christofteuscher/TrailNapAlarm/openchoice/Limiter50ohm10mVpp.bmp

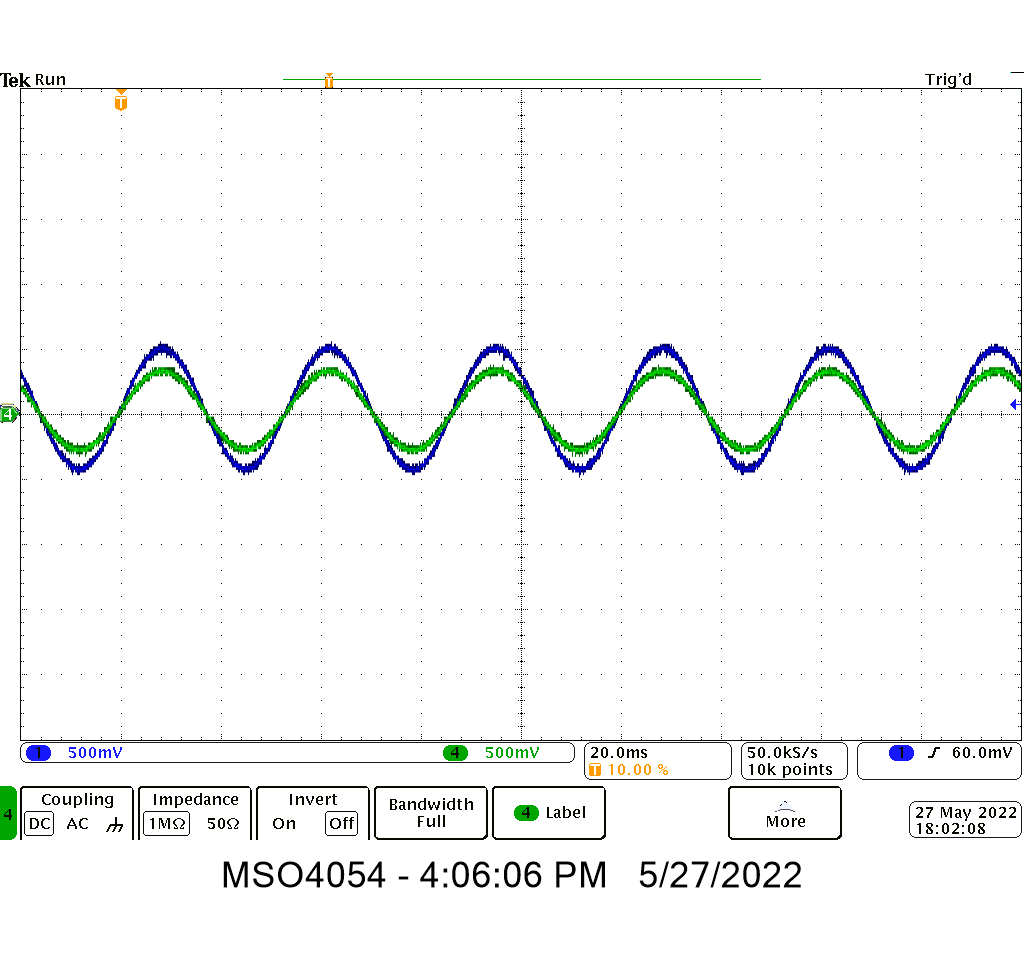
openchoice/Limiter50ohm10mVpp.bmp
