christofteuscher/TrailNapAlarm/res/figures/docFigs/AD620_example.png

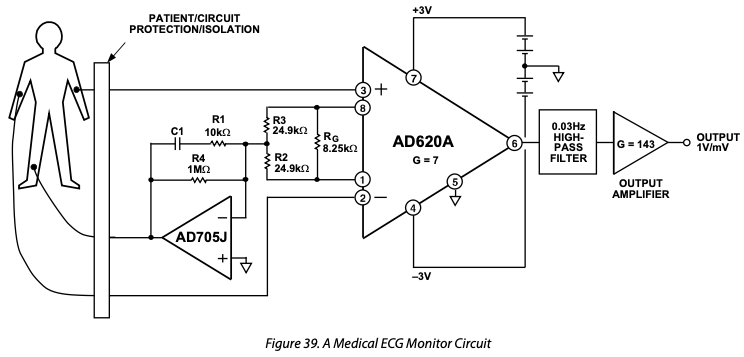
res/figures/docFigs/AD620_example.png
