christofteuscher/TrailNapAlarm/res/figures/docFigs/adc_breakout_connections.PNG

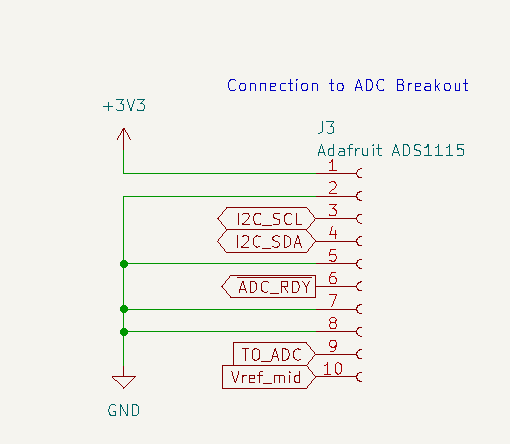
res/figures/docFigs/adc_breakout_connections.PNG
