christofteuscher/TrailNapAlarm/res/figures/docFigs/amplifier-filter.png

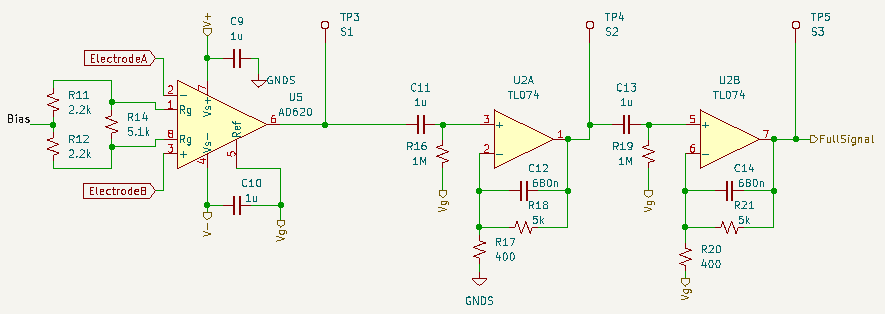
res/figures/docFigs/amplifier-filter.png
