christofteuscher/TrailNapAlarm/res/figures/docFigs/CapstoneEEGL0_L1.png

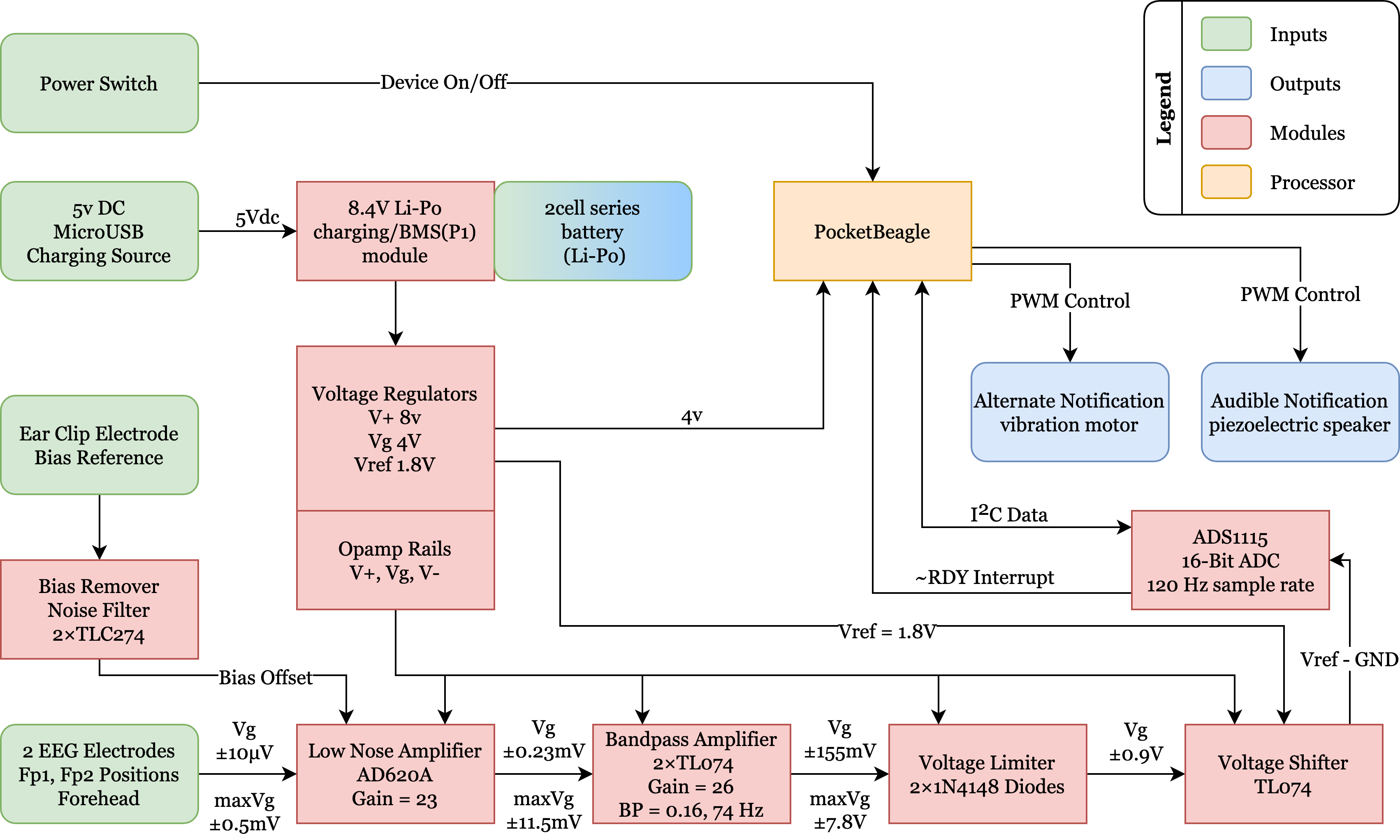
res/figures/docFigs/CapstoneEEGL0_L1.png
