christofteuscher/TrailNapAlarm/res/figures/docFigs/comparisonfig.png

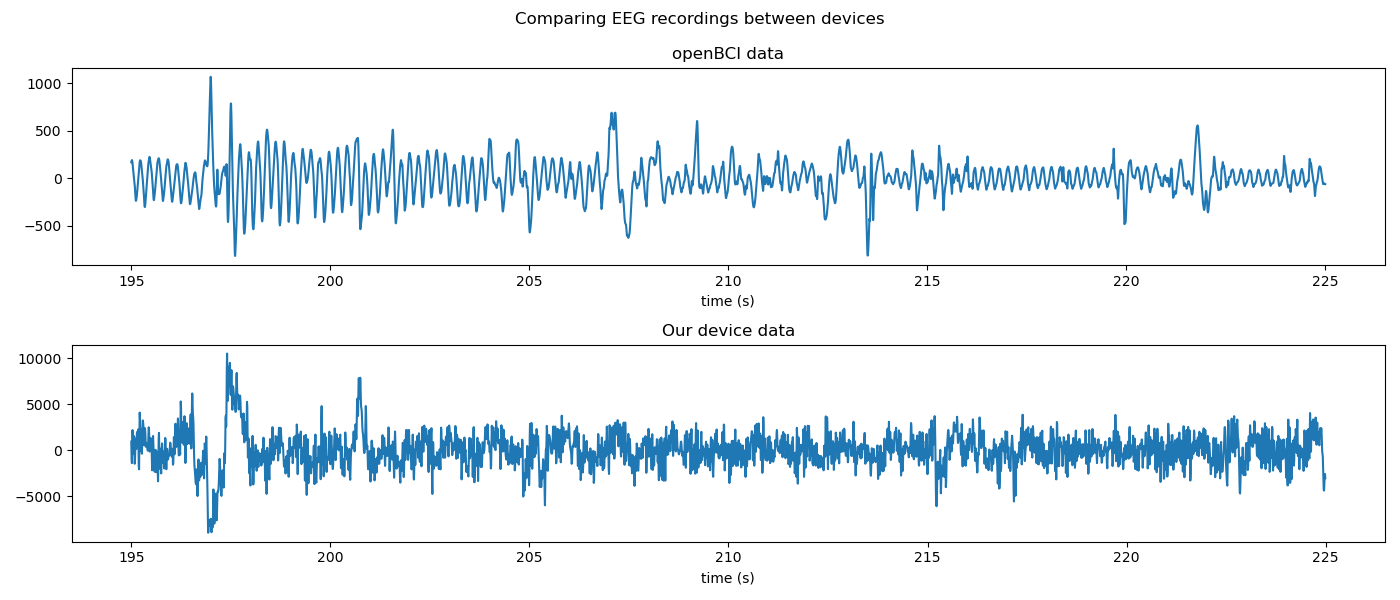
res/figures/docFigs/comparisonfig.png
