christofteuscher/TrailNapAlarm/res/figures/docFigs/dataFlowDiag.png

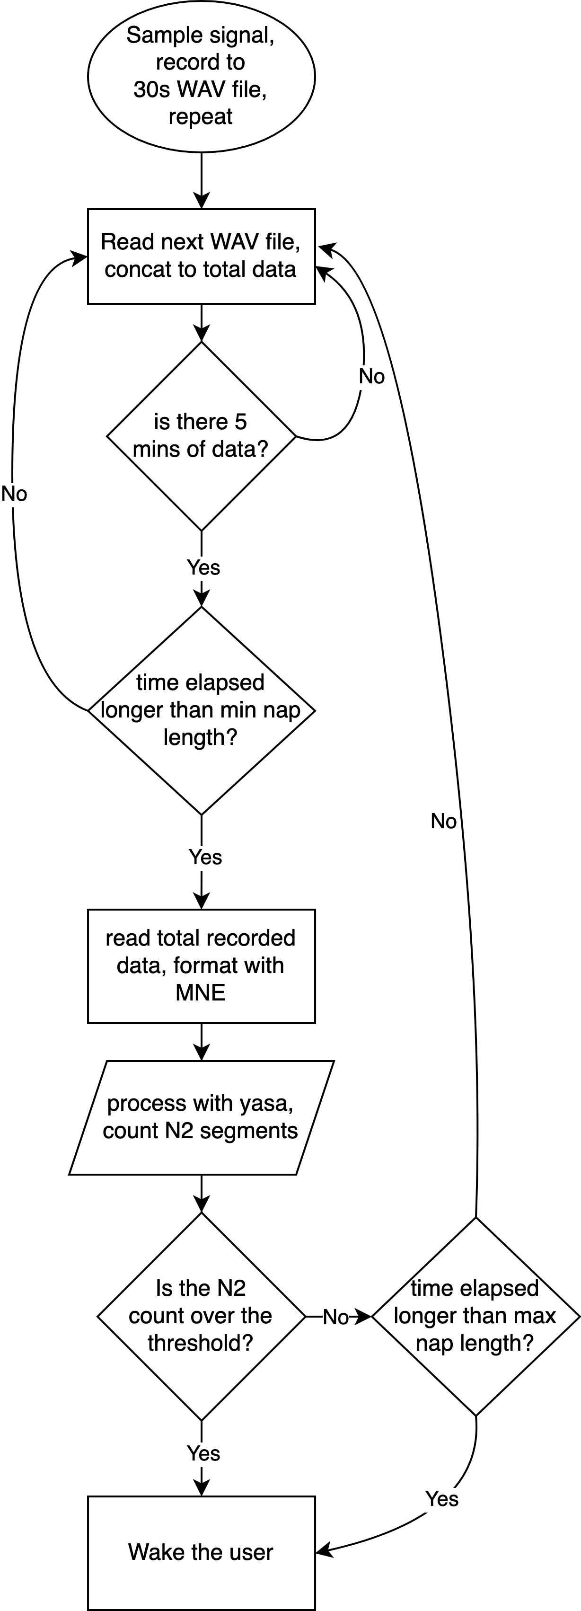
res/figures/docFigs/dataFlowDiag.png
