christofteuscher/TrailNapAlarm/res/figures/docFigs/drl_ckt.png

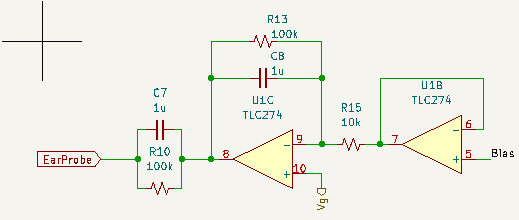
res/figures/docFigs/drl_ckt.png
