christofteuscher/TrailNapAlarm/res/figures/docFigs/EEG.png

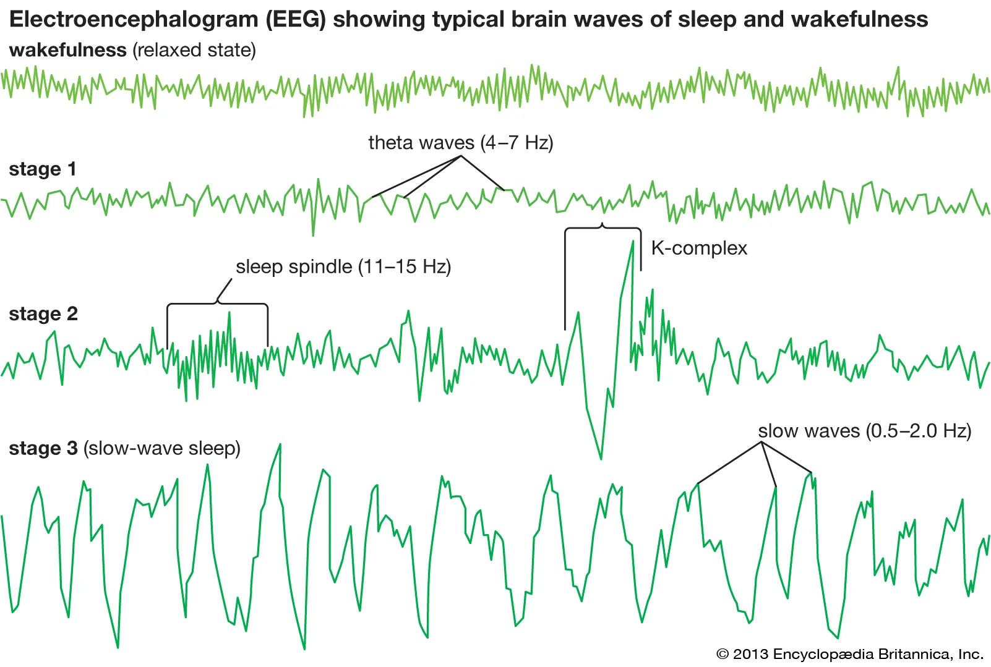
res/figures/docFigs/EEG.png
