christofteuscher/TrailNapAlarm/res/figures/docFigs/power_rails.PNG

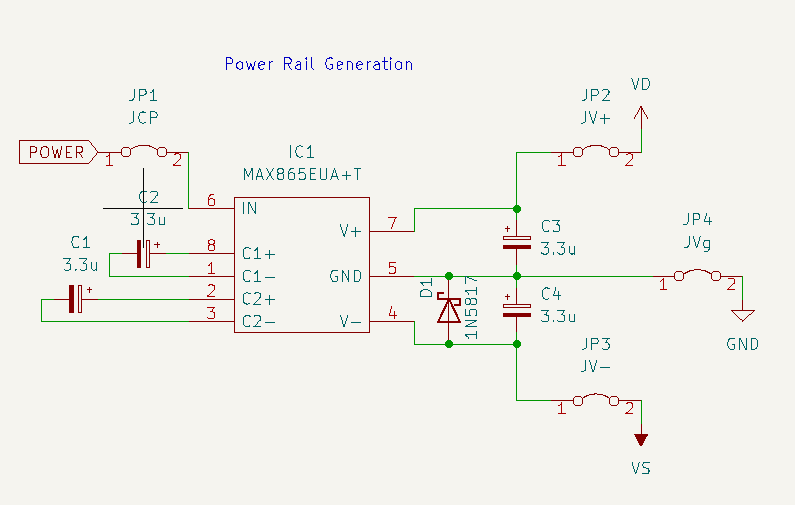
res/figures/docFigs/power_rails.PNG
