christofteuscher/TrailNapAlarm/res/figures/docFigs/spindledetect.png

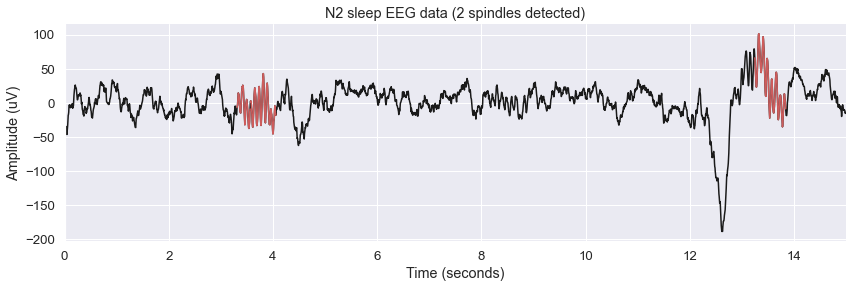
res/figures/docFigs/spindledetect.png
