christofteuscher/TrailNapAlarm/res/figures/docFigs/teuscherlab.png

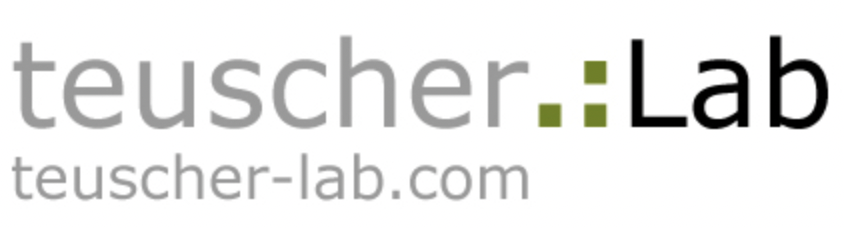
res/figures/docFigs/teuscherlab.png
