christofteuscher/TrailNapAlarm/res/figures/docFigs/timeseries_stages.png

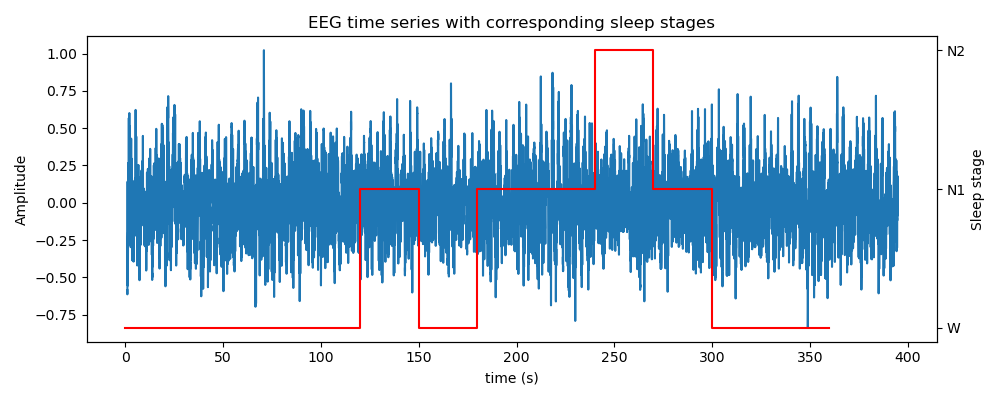
res/figures/docFigs/timeseries_stages.png
