christofteuscher/TrailNapAlarm/res/figures/docFigs/voltageshifter.png

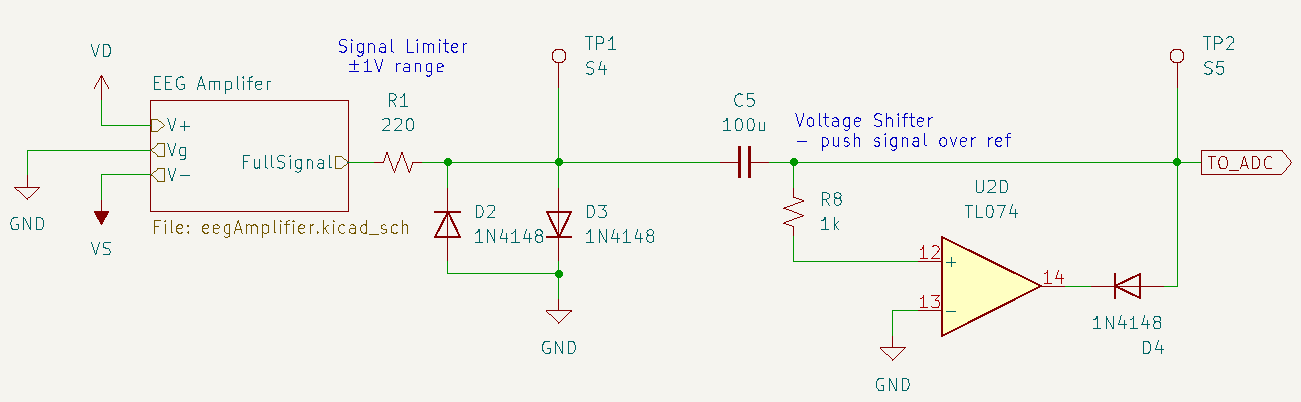
res/figures/docFigs/voltageshifter.png
