christofteuscher/TrailNapAlarm/res/figures/exampleYasafigs/Fz_10_movcorrel.png

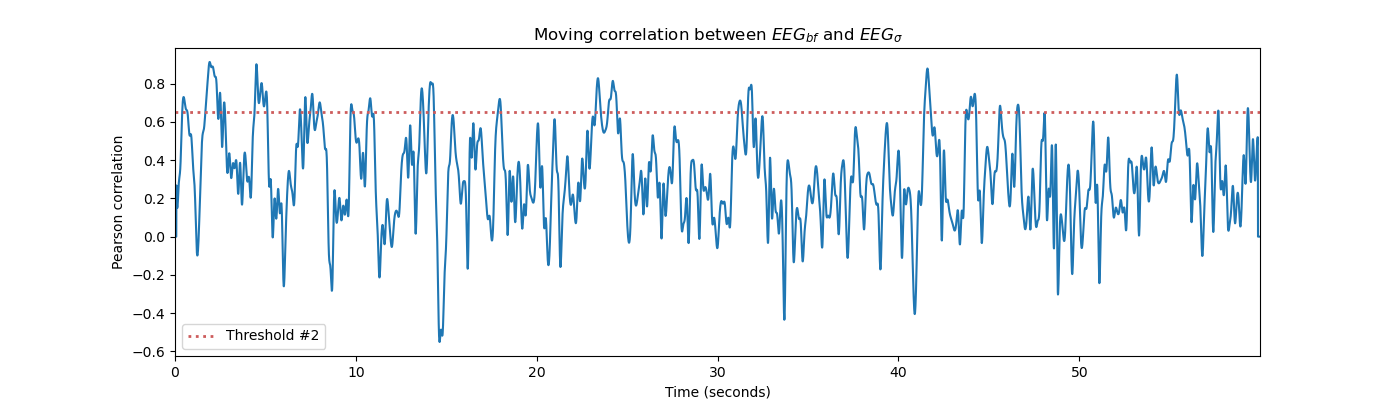
res/figures/exampleYasafigs/Fz_10_movcorrel.png
