christofteuscher/TrailNapAlarm/res/figures/exampleYasafigs/Fz_10_sigma_rel_power.png

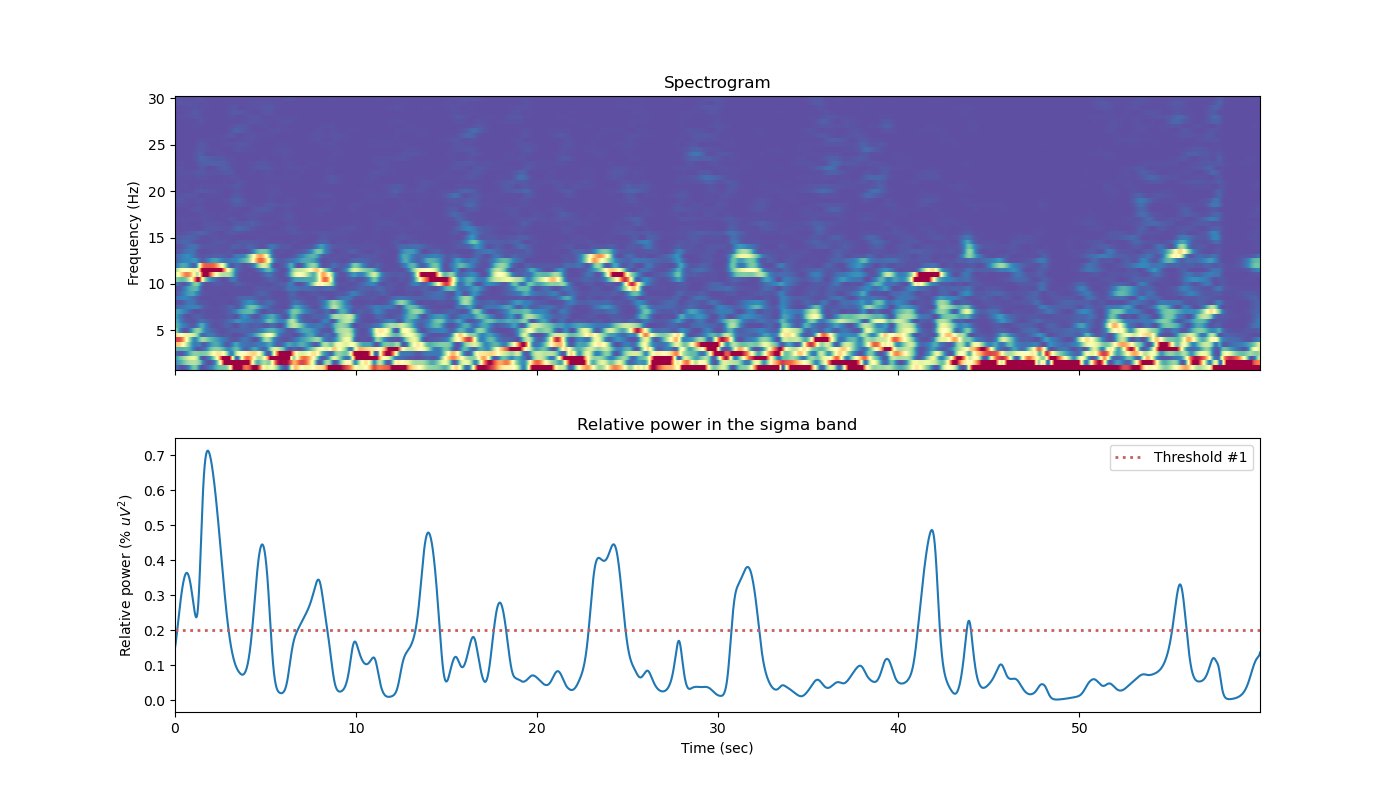
res/figures/exampleYasafigs/Fz_10_sigma_rel_power.png
