christofteuscher/TrailNapAlarm/res/figures/exampleYasafigs/Fz_10_timeseries.png

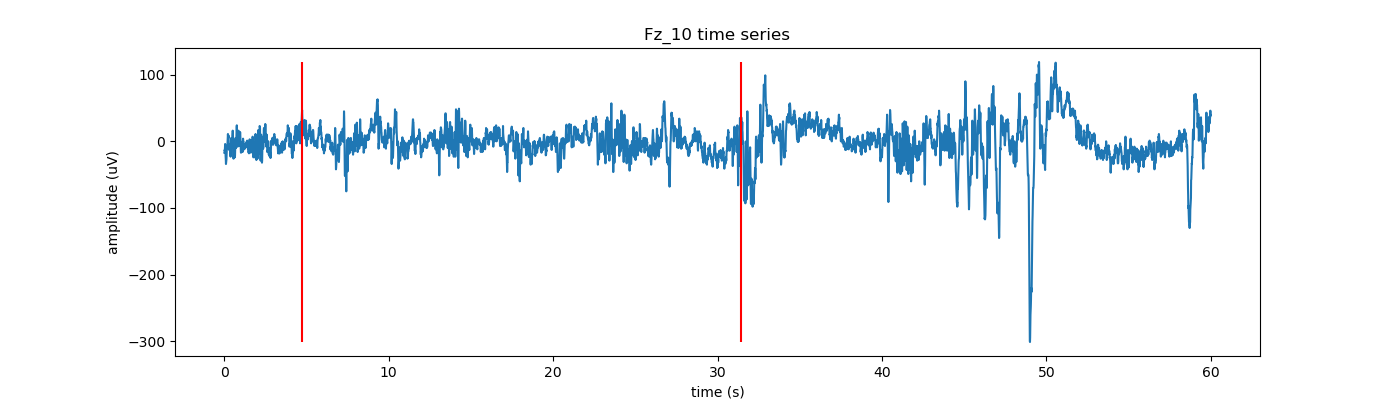
res/figures/exampleYasafigs/Fz_10_timeseries.png
