christofteuscher/TrailNapAlarm/openchoice/TestCheckClamperOutput.bmp

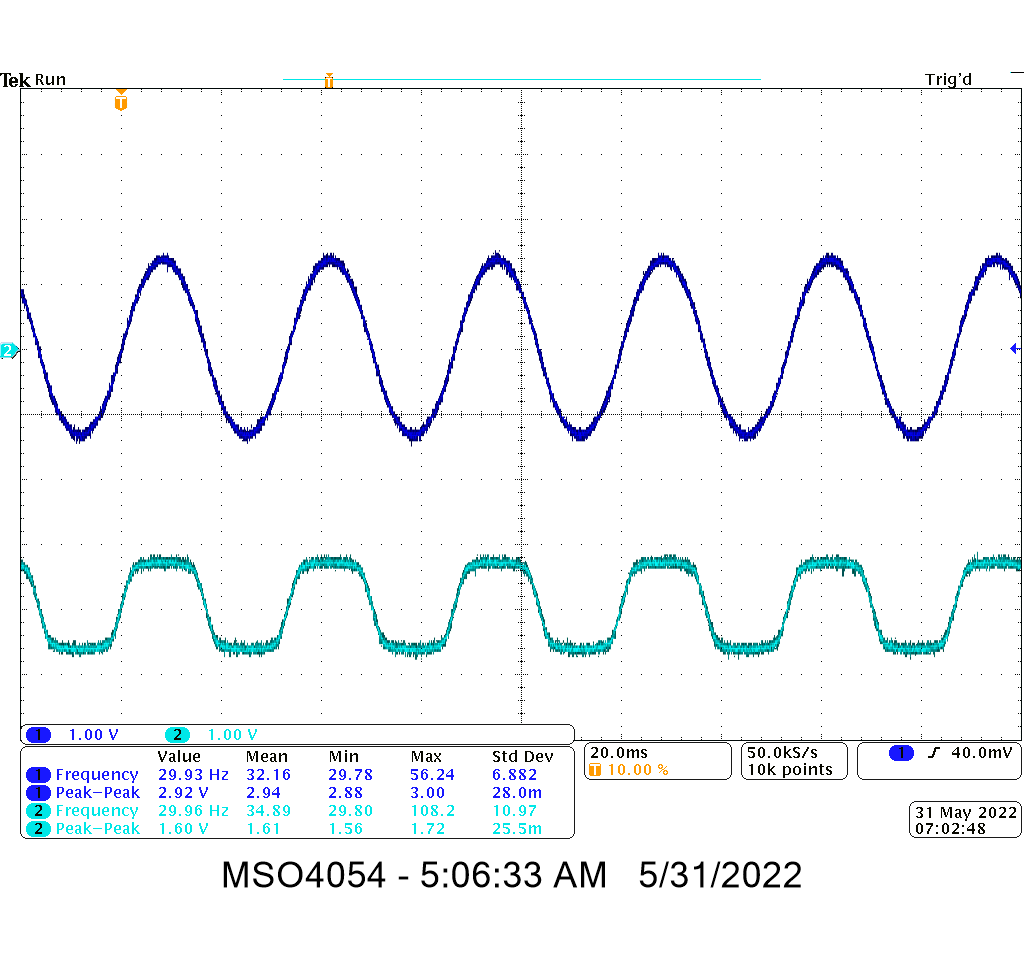
openchoice/TestCheckClamperOutput.bmp
