christofteuscher/TrailNapAlarm/openchoice/TestInputBase.bmp

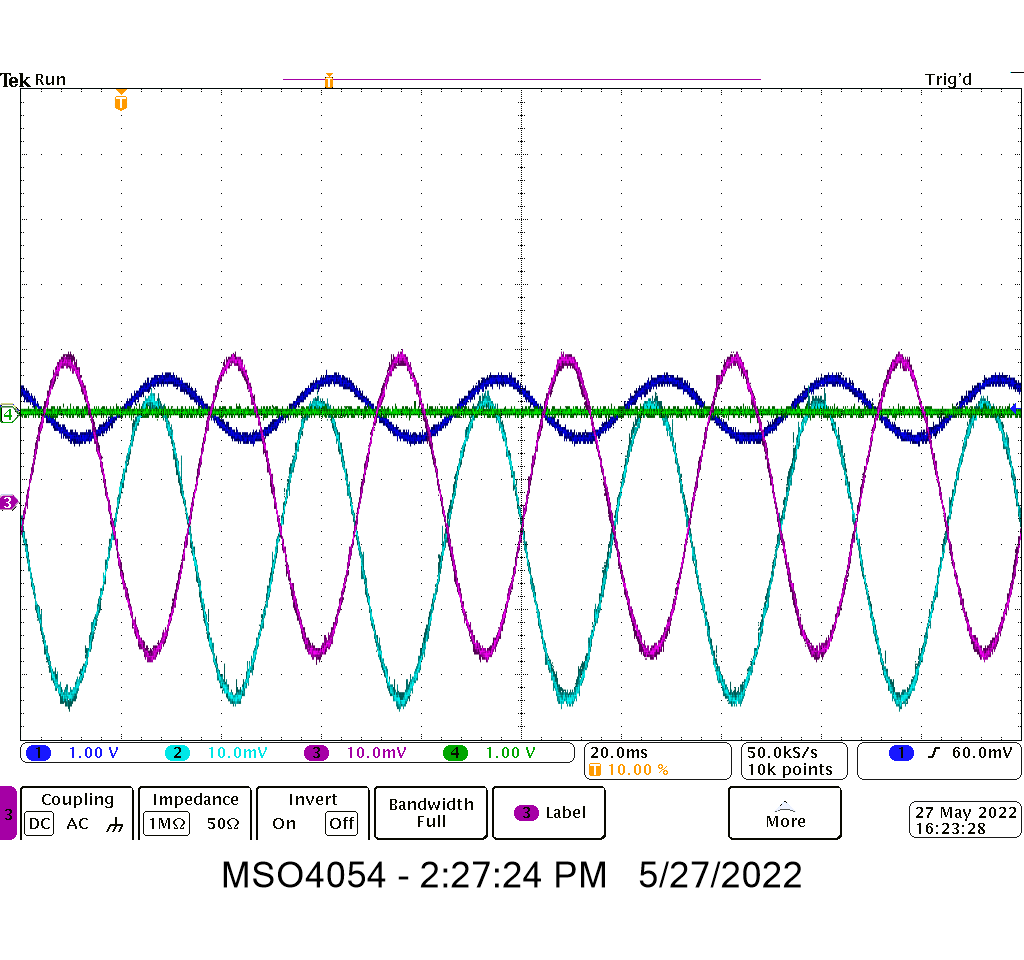
openchoice/TestInputBase.bmp
