christofteuscher/TrailNapAlarm/openchoice/TestInputBaseLimiter.bmp

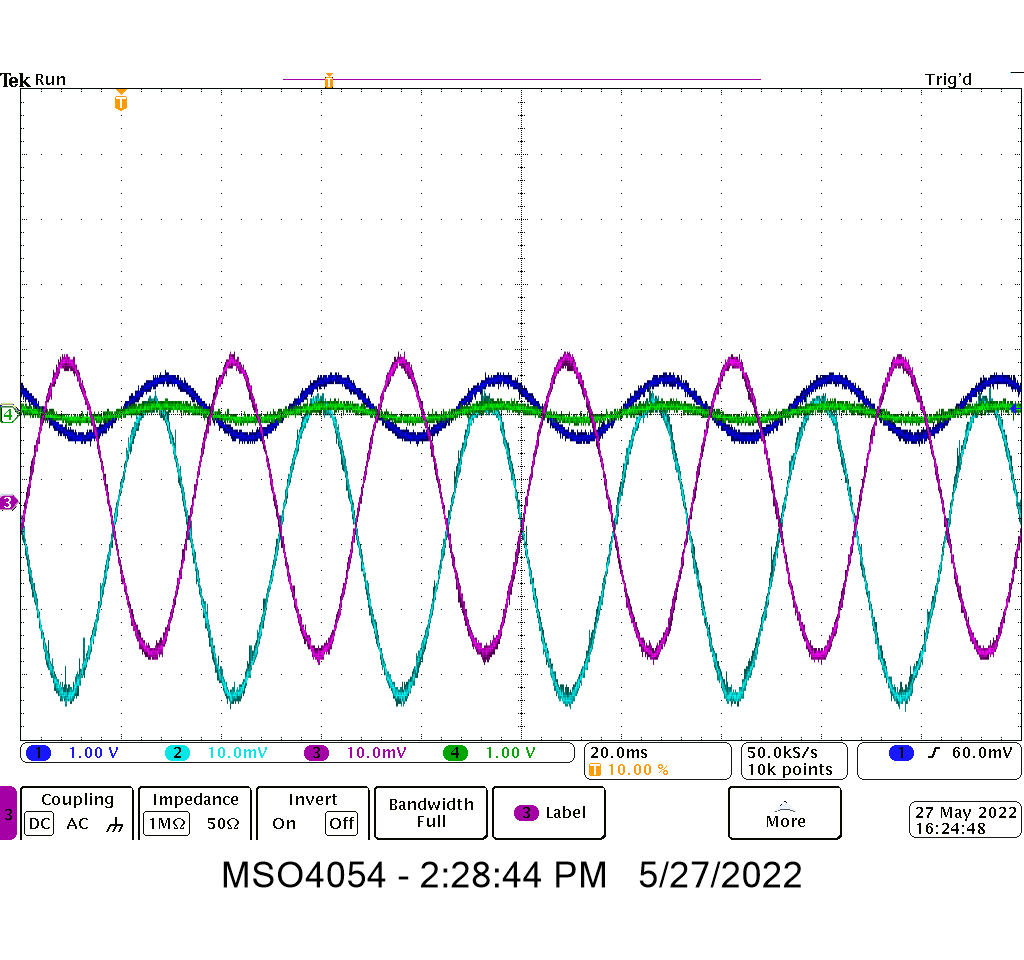
openchoice/TestInputBaseLimiter.bmp
