christofteuscher/TrailNapAlarm/res/figures/docFigs/algo_results.png

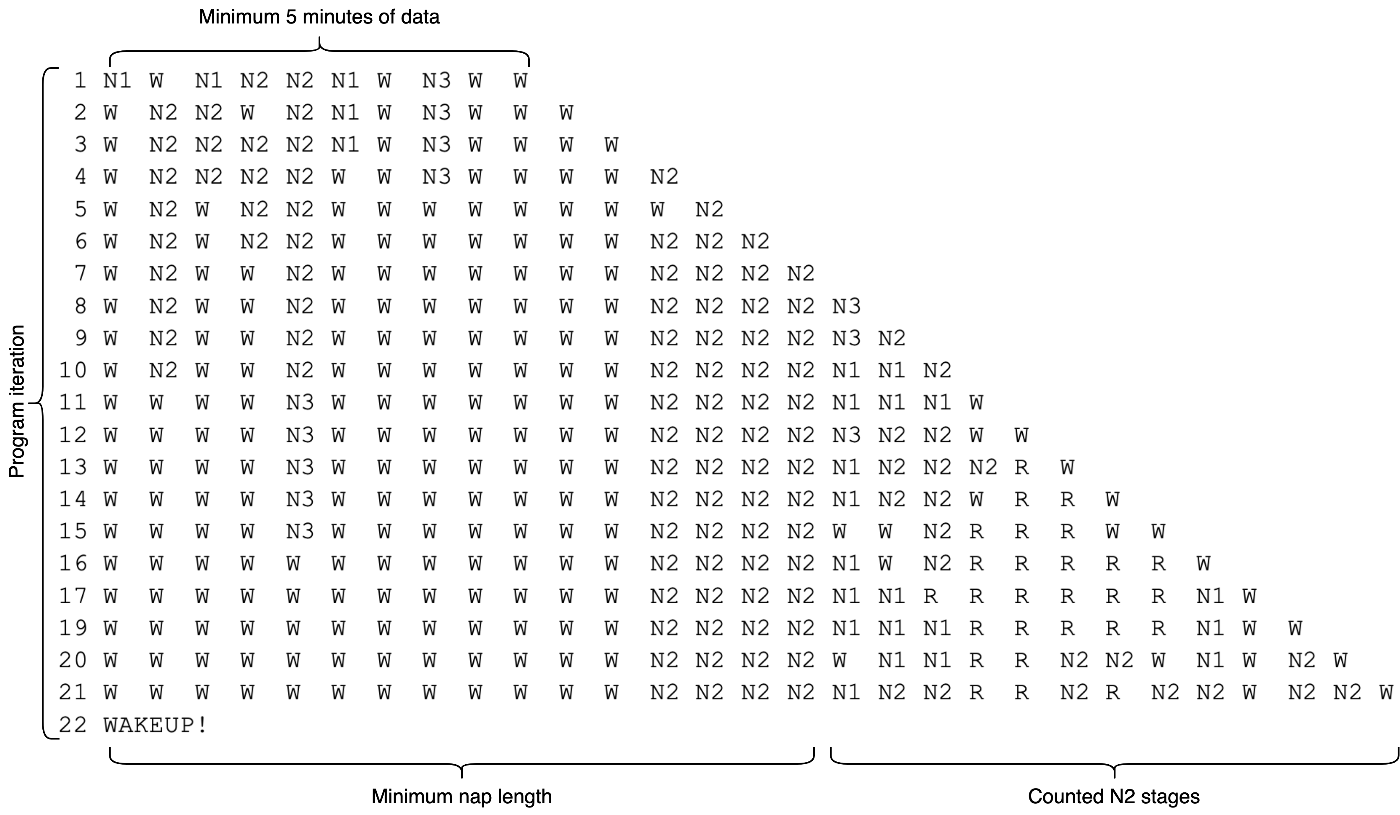
res/figures/docFigs/algo_results.png
