christofteuscher/TrailNapAlarm/res/figures/docFigs/openbci_algo_results.png

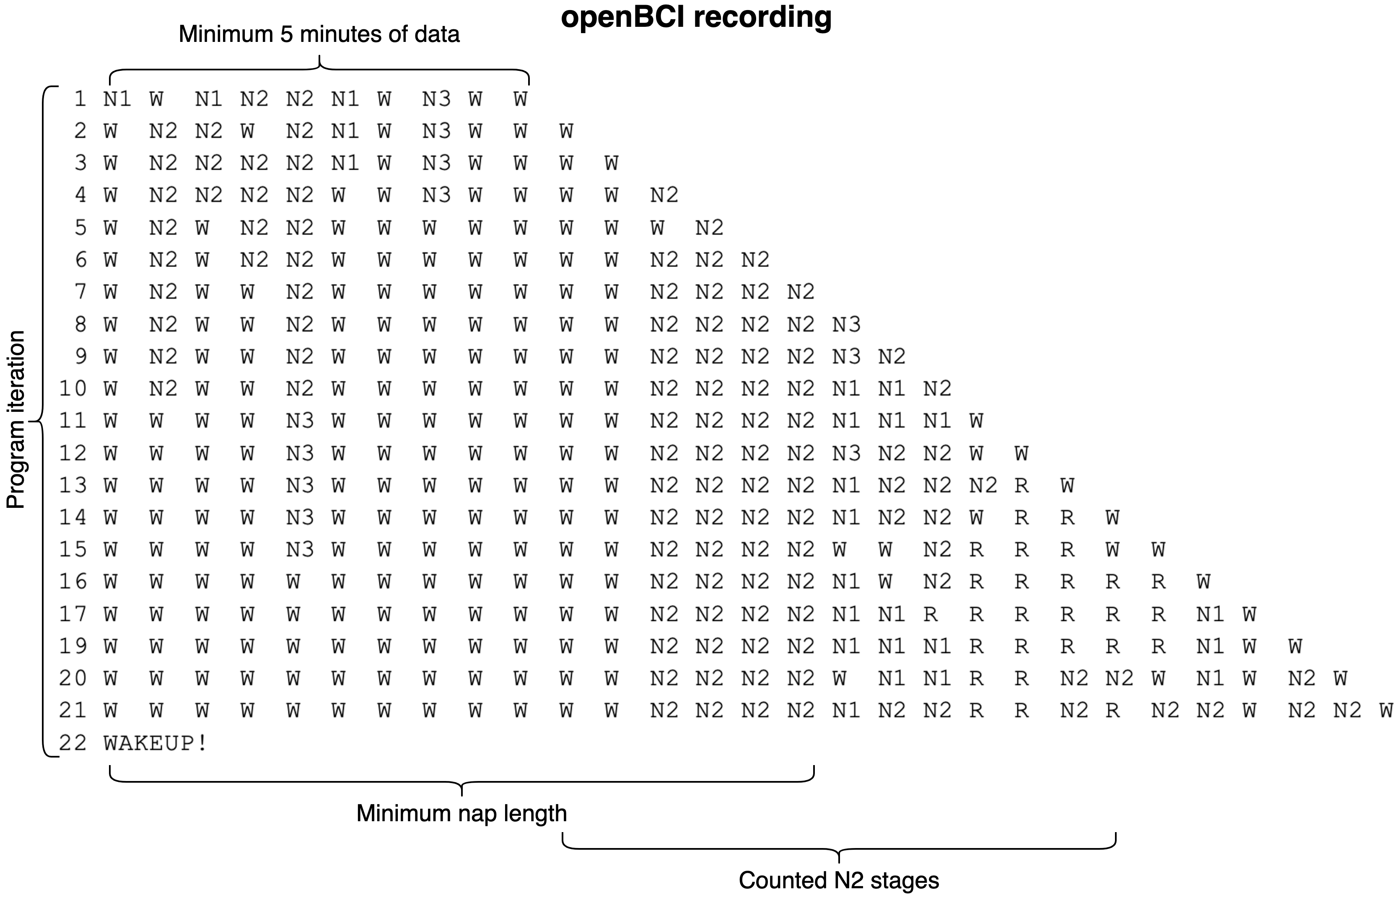
res/figures/docFigs/openbci_algo_results.png
