christofteuscher/TrailNapAlarm/res/figures/docFigs/Ourdevice_algo_results2.png

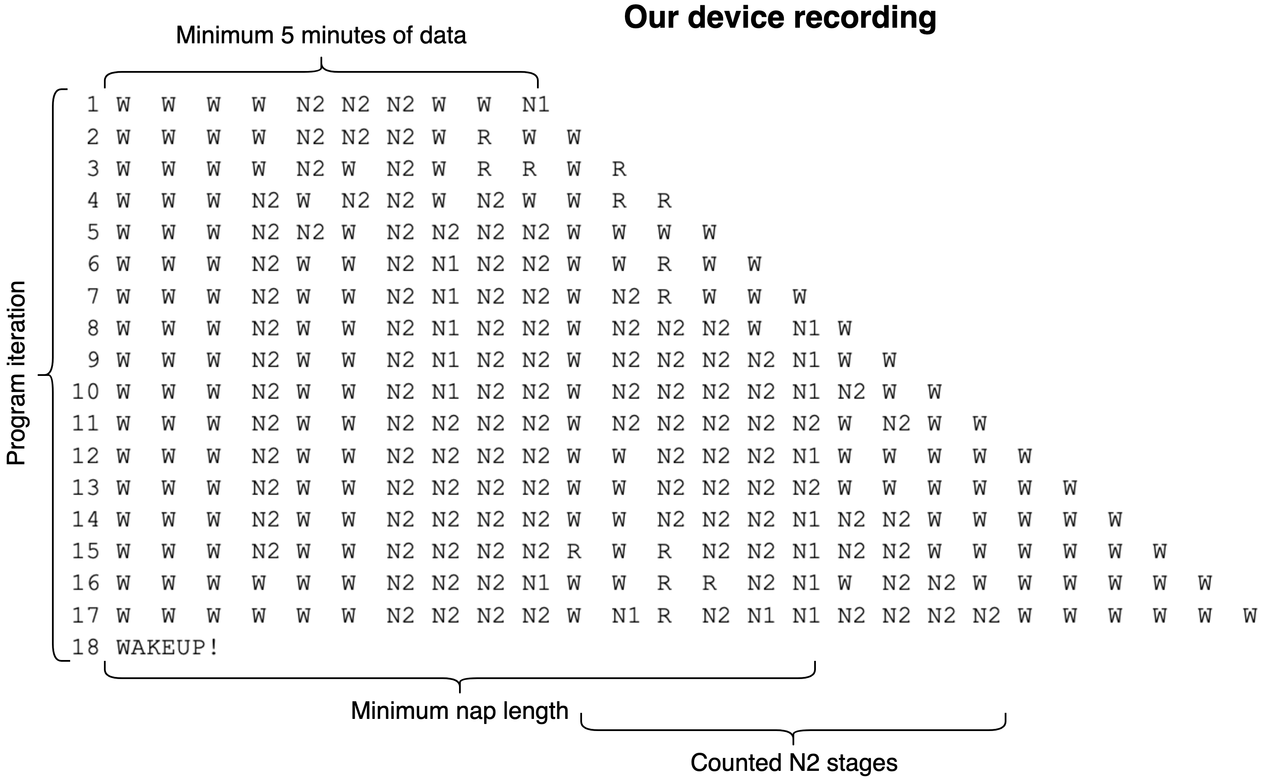
res/figures/docFigs/Ourdevice_algo_results2.png
