christofteuscher/TrailNapAlarm/ltspice/capstone_clamp_testing.asc

C1: cap; {C}
C2: cap; {C}
C3: cap; {C}
C4: cap; {C}
C5: cap; {C}
D1: diode; 1N4148
D2: diode; 1N4148
D3: diode; 1N4148
D4: diode; 1N4148
D6: diode; 1N4148
D7: diode; 1N4148
D8: zener; 1N750
D9: zener; 1N750
D10: diode; 1N4148
R1: res; {R}
R2: res; {R}
R3: res; {R}
R6: res; {R}
R7: res; 200
R10: res; 220
R11: res; {R}
U1: UniversalOpamp2
U2: UniversalOpamp2
U4: UniversalOpamp2
V1: voltage; SINE(0 3.3 47); AC 5
V2: voltage; {Vcc}
V3: voltage; 5
V5: voltage; 1.8
Named nets: Vin+, OUT_ppu, ref, V+, V-, OUT_ap, OUT_an, 0, Vin-, OUT_pnu, OUT_test2, Vin_clamped, OUT_final, Vg
.tran 100m startup
.param Vcc=10 hpHz=50 R=1k C=1u D=1N4148
Active Positive Clamper
Active Negative Clamper
Passive Positive Unbiased
Passive Negative Unbiased
;.ac dec 100 0.10 120
