christofteuscher/TrailNapAlarm/ltspice/diode_test.asc

D1: zener; DZlim2
D2: zener; 1N750
R1: res; 1k
R2: res; 1k
V1: voltage; 1
Named nets: 0, D1
.model DZlim2 D(Ron=1 Roff=1Meg Vfwd=0.7 Vrev=4.7)
.dc V1 -10 10 0.1
Generating IV plot for diode
