christofteuscher/TrailNapAlarm/ltspice/capstone_all.asc

R1: res; 101
R2: res; 10k
R3: res; 101
R4: res; 10k
V1: voltage; 1
V2: voltage; 1
Named nets: TEST_INPUT-, TEST_INPUT+, 0
Test Signal
±20µV
.op
Test Signal
±20µV
