christofteuscher/TrailNapAlarm/ltspice/capstone_clamp.asc

C1: cap; {C}
C2: cap; {C}
D1: diode; 1N4148
D2: diode; 1N4148
D3: diode; 1N4148
D4: diode; 1N4148
R1: res; 220
R2: res; {R}
R3: res; {R}
U1: UniversalOpamp2
U2: UniversalOpamp2
V1: voltage; SINE(0 3.3 47); AC 5
V2: voltage; 10
V3: voltage; 5
V4: voltage; 1.8
V5: voltage; 5.7
Named nets: Vin+, V+, V-, Vg, Vin_clamped, OUT_final, 0, OUT_extra
.tran 200m startup
.param hpHz=0.16 R=1k C=100u
;.ac oct 100 0.16 120 100 0.16 120
