christofteuscher/TrailNapAlarm/ltspice/capstone_clamp_final.asc

D1: diode; 1N4148
D2: diode; 1N4148
R1: res; 1k
V1: voltage; {3.7 * 2}
V2: voltage; 10
V3: voltage; 5
V4: voltage; {V(Vg) - 1.65}
V5: voltage; SINE(0 5 30)
Named nets: OUT_clamped, Vbat+, Vbat-, V+, V-, Vg, Vadc-, 0, Vin
Clamp Signal before ADC
- Must have current below 200mA
.tran 100m
