christofteuscher/TrailNapAlarm/ltspice/capstone_divider_supply.asc

C1: cap; 0.1µ
C2: cap; 0.1µ
R1: res; 2k
R2: res; 2k
V1: voltage; 3.3
Named nets: 0
Initial power supply on breadboard design.
