christofteuscher/TrailNapAlarm/ltspice/capstone_filter_only.asc

C1: cap; 1µ
C2: cap; 680n
C3: cap; 340n
C4: cap; 100µ
C5: cap; 200µ
C6: cap; 680n
C7: cap; 320n
C8: cap; 100µ
R1: res; 1Meg
R2: res; 5k
R3: res; 200
R4: res; 10k
R5: res; 10k
R6: res; 10k
R7: res; 5k
R8: res; 5k
R9: res; 10k
U1: opamp2; TL074
U2: opamp2; TL074
U3: opamp2; TL074
U4: opamp2; TL074
V1: voltage; SINE(); AC 1
V2: voltage; 3.3
V3: voltage; 3.3
V4: voltage; SINE(); AC 1
Named nets: V+, v-, OUT, 0, IN, OUT_fil, HP_def, IN2, OUT_fil2, OUT_fil_actual
.lib TL074.301.lib
.ac dec 1000 0.1 100
