christofteuscher/TrailNapAlarm/ltspice/capstone_rails_bb.asc

R1: res; 270
R2: res; 1.9k
R3: res; 270
R4: res; 828
R5: res; 270
R6: res; 463.6
U1: LM317
U2: LM317
U3: LM317
V1: voltage; 12
V2: voltage; 3.3
Named nets: Vbat+, V+, Vg, Vref, Vbat-, V3.3, 0
.op
BeaglePocket
Onboard 3.3v regulator
Voltage Rails Testing for Breadboard Design
