christofteuscher/TrailNapAlarm/ltspice/EEGTestCircuit1WithNoise.asc

B1: bv; V=(white(2e6*time) / 1000000)
C1: cap; 1µ
C2: cap; 680n
C3: cap; 1µ
C4: cap; 680n
C5: cap; 1µ
C6: cap; 1µ
C7: cap; 1000p
C8: cap; 1000p
C9: cap; 680n
C10: cap; 200µ
Electrode1: voltage; SINE(0 50e-6 20 1n 1n 15)
Electrode2: voltage; SINE(0 50e-6 20 1n 1n 15)
R1: res; 5k
R2: res; 1Meg
R3: res; 200
R4: res; 1Meg
R5: res; 5k
R6: res; 200
R7: res; 5.1k
R8: res; 2.2k
R9: res; 100k
R10: res; 2.2k
R11: res; 10k
R12: res; 100k
R13: res; 10
R14: res; 10k
R15: res; 100k
R16: res; 1k
R17: res; 1k
R18: res; 1k
R19: res; 5k
R20: res; 5k
Reference: voltage; SINE(0 0 200 1n 1n 15); AC 0
U1: opamp2; TL074
U2: opamp2; TL074
U3: opamp2; TLC274
U4: opamp2; TLC274
U5: opamp2; TL074
U6: ad620; AD620B
V1: voltage; 2.4
V2: voltage; 7.2
Named nets: 0, 2V, V+, reference, out, Electrode1, Electrode2, NOISE, v-, OUT_amp, Vg
.lib lib/TL074.301
.tran 0 10 0 100m
.options plotwinsize = 0
.lib lib/TLC274.5_1
.include lib/lude lib/ad620b.cir
