christofteuscher/TrailNapAlarm/ltspice/voltage_reference_pot.asc

R1: res; 10.45k
R2: res; 3.8k
U1: pot; R=10k
V1: voltage; 3.3
Named nets: 0, Vref
.param adj=0.5
.step param adj 0 1 0.1
.op
