christofteuscher/TrailNapAlarm/src/buildRaw.py

import mne
import numpy as np
from scipy.io.wavfile import read

# this file loads data into an raw mne format
# storing data like this allows us to include metadata in a way
# that can be implemented with mne functions and saved as an edf file

scaleFactor = 20e-6

def buildRawFromNpz(fs, filepath):

    # load data
    x = np.load(filepath)
    data, chan_names = x['data'], x['chan']
    num_chan = data.shape[0]

    # verify data
    #print(data.shape, chan_names)
    #print(np.round(data[:, 0:5], 3))

    # create metadata for raw edf
    ch_names = []
    for name in chan_names:
        ch_names.append(f"{name}")
    ch_types = ['eeg'] * num_chan
    info = mne.create_info(ch_names, ch_types=ch_types, sfreq=fs)
    # standard spatial orientation based on channel names
    info.set_montage('standard_1020')

    # save as raw format
    raw = mne.io.RawArray(data, info, verbose='warning')

    # sample data is not in SI units, which is what mne raw expects
    # we have to scale the data to the expected uV range
    raw.apply_function(lambda x: x * scaleFactor)

    return raw

def buildRawFromWav(filepath):
    # read sample freq and data from file
    fs, data = read(filepath)
    data = [data,data]

    num_chan = 2
    ch_names = ['Fz', 'Fp1']
    ch_types = ['eeg'] * num_chan
    info = mne.create_info(ch_names, ch_types=ch_types, sfreq=fs)
    # standard spatial orientation based on channel names
    info.set_montage('standard_1020')

    # save as raw format
    raw = mne.io.RawArray(data, info, verbose='warning')

    # sample data is not in SI units, which is what mne raw expects
    # we have to scale the data to the expected uV range
    raw.apply_function(lambda x: x * scaleFactor)

    return raw

def buildRawFromArray(fs, array):
    array = [array,array]

    num_chan = 2
    ch_names = ['Fz', 'Fp1']
    ch_types = ['eeg'] * num_chan
    info = mne.create_info(ch_names, ch_types=ch_types, sfreq=fs)
    # standard spatial orientation based on channel names
    #info.set_montage('standard_1020')

    # save as raw format
    raw = mne.io.RawArray(array, info, verbose='warning')

    # sample data is not in SI units, which is what mne raw expects
    # we have to scale the data to the expected uV range
    raw.apply_function(lambda x: x * scaleFactor)

    return raw
